andrewpatcarr/CV_OrigamiRobot_Fall2024/log_photos/joystick_arduino_housing.jpg

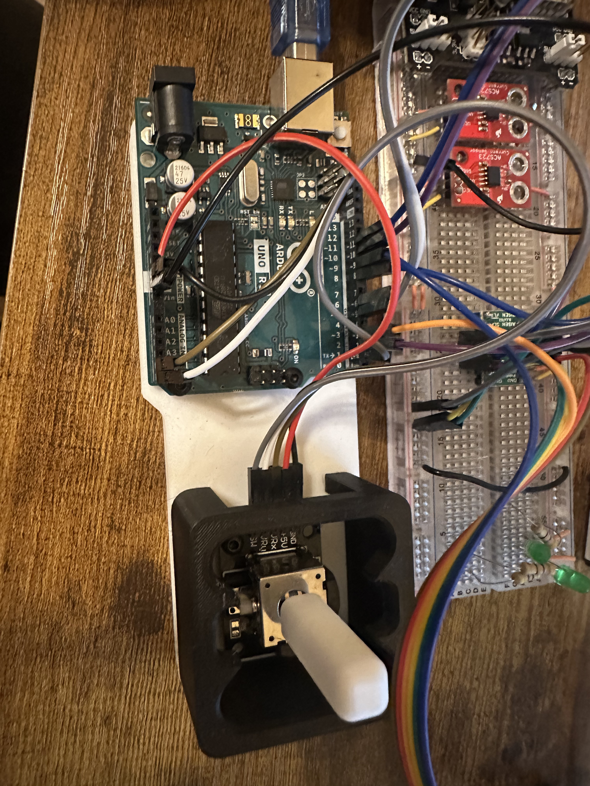
log_photos/joystick_arduino_housing.jpg
