andrewpatcarr/CV_OrigamiRobot_Fall2024/log_photos/motor_driver_screenshot_wordless.png

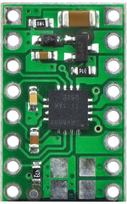
log_photos/motor_driver_screenshot_wordless.png
