andrewpatcarr/CV_OrigamiRobot_Fall2024/CAD/STLs/Friction Pads/Friction_straightangled_thinner^Worm_Robot.STL

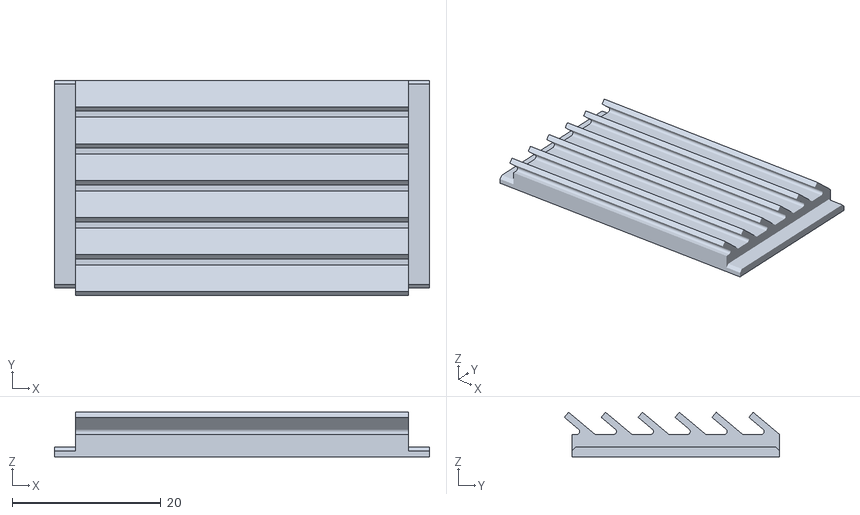
[picture p86: CAD file, 2024-11-07]
CAD/STLs/Friction Pads/Friction_straightangled_thinner^Worm_Robot.STL
50.5 x 29.0 x 6.00
