andrewpatcarr/CV_OrigamiRobot_Fall2024/CAD/SolidWorks/Pulley Horn^Worm_Robot.SLDPRT

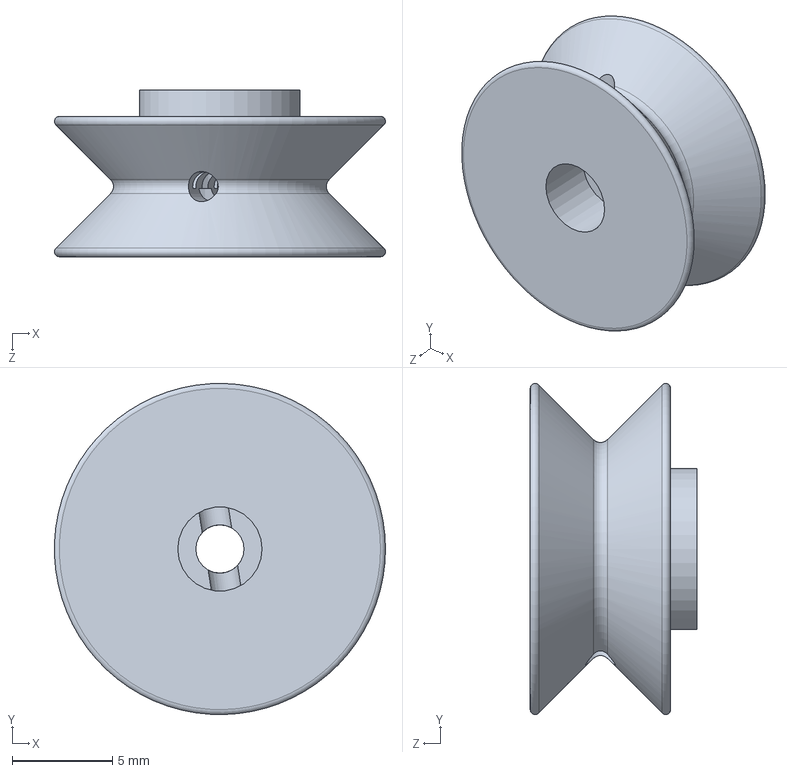
[picture p87: CAD file, 2024-10-20]
CAD/SolidWorks/Pulley Horn^Worm_Robot.SLDPRT
16.5 x 16.5 x 8.30 mm
