andrewpatcarr/CV_OrigamiRobot_Fall2024/CAD/SolidWorks/FS09R_Servo_Motor.SLDPRT

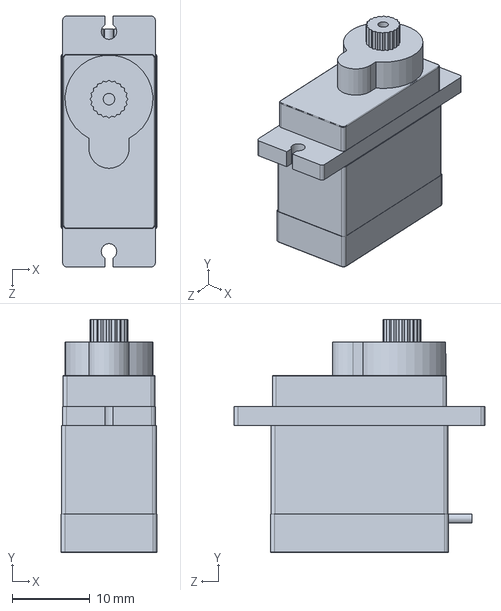
[picture p89: CAD file, 2024-10-16]
CAD/SolidWorks/FS09R_Servo_Motor.SLDPRT
12.3 x 30.0 x 32.2 mm
