andrewpatcarr/CV_OrigamiRobot_Fall2024/CAD/STLs/Friction Pads/Friction_straightangled_thinnest^Worm_Robot.STL

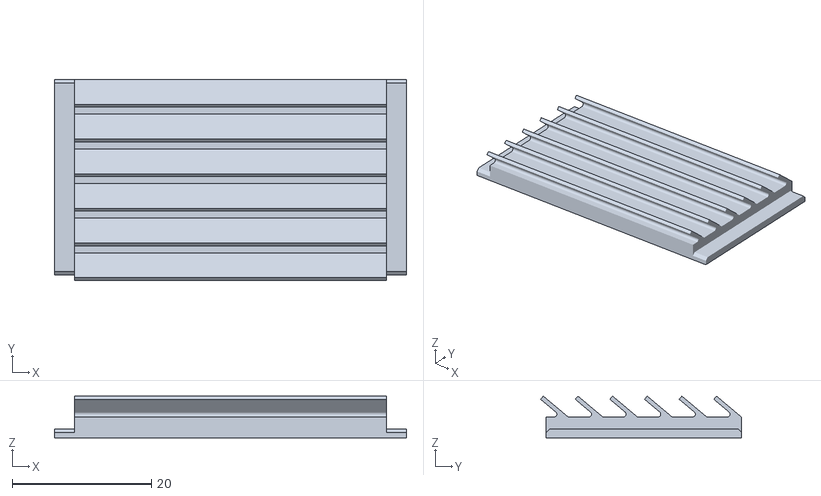
[picture p90: CAD file, 2024-11-07]
CAD/STLs/Friction Pads/Friction_straightangled_thinnest^Worm_Robot.STL
50.5 x 28.8 x 6.00
