andrewpatcarr/CV_OrigamiRobot_Fall2024/CAD/SolidWorks/Directional Friction Flexure_less.SLDPRT

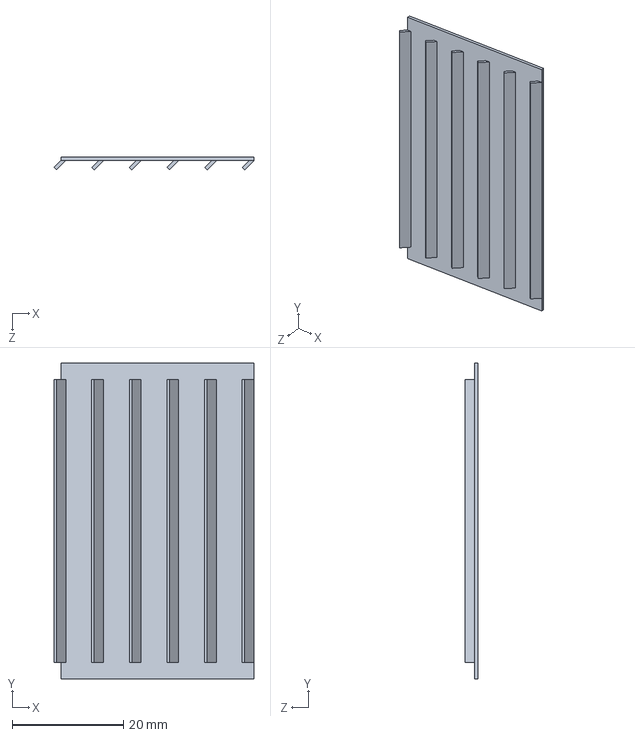
[picture p91: CAD file, 2024-10-15]
CAD/SolidWorks/Directional Friction Flexure_less.SLDPRT
35.9 x 56.8 x 2.30 mm
