andrewpatcarr/CV_OrigamiRobot_Fall2024/CAD/SolidWorks/Directional Friction Flexure.sldprt

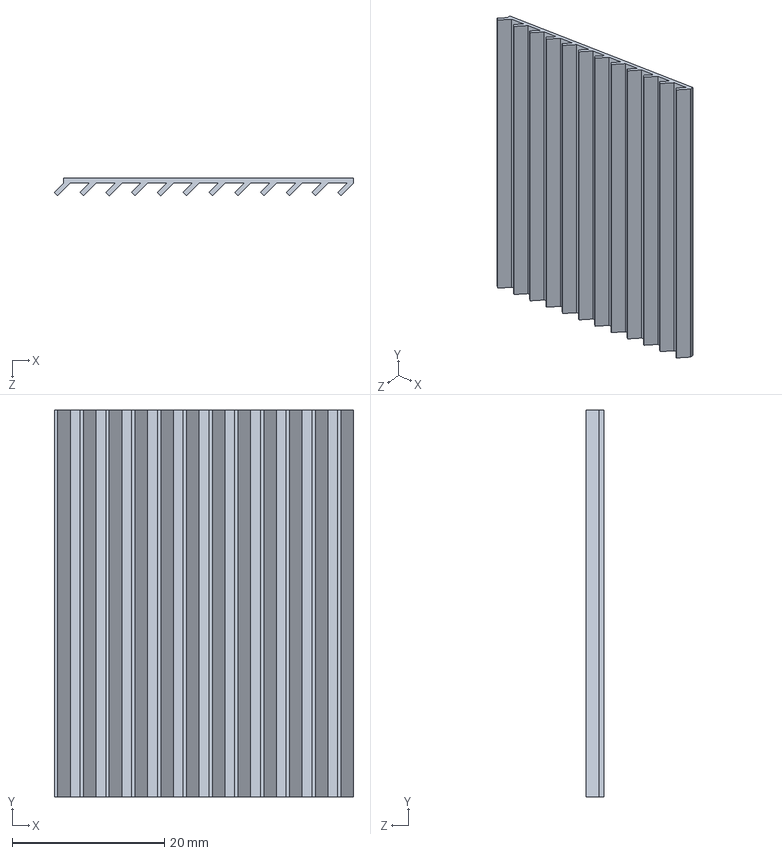
[picture p92: CAD file, 2024-10-14]
CAD/SolidWorks/Directional Friction Flexure.sldprt
39.3 x 50.8 x 2.30 mm
