andrewpatcarr/CV_OrigamiRobot_Fall2024/CAD/STLs/Mount Clamp Left^Worm_Robot.STL

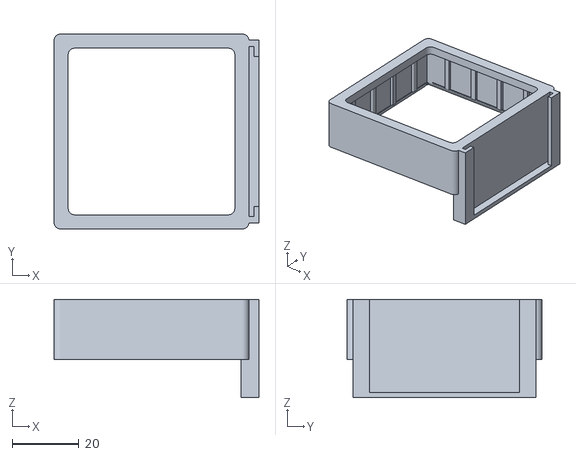
[picture p93: CAD file, 2024-10-19]
CAD/STLs/Mount Clamp Left^Worm_Robot.STL
61.5 x 58.5 x 29.5
