andrewpatcarr/CV_OrigamiRobot_Fall2024/CAD/SolidWorks/Directional Friction Pad.sldprt

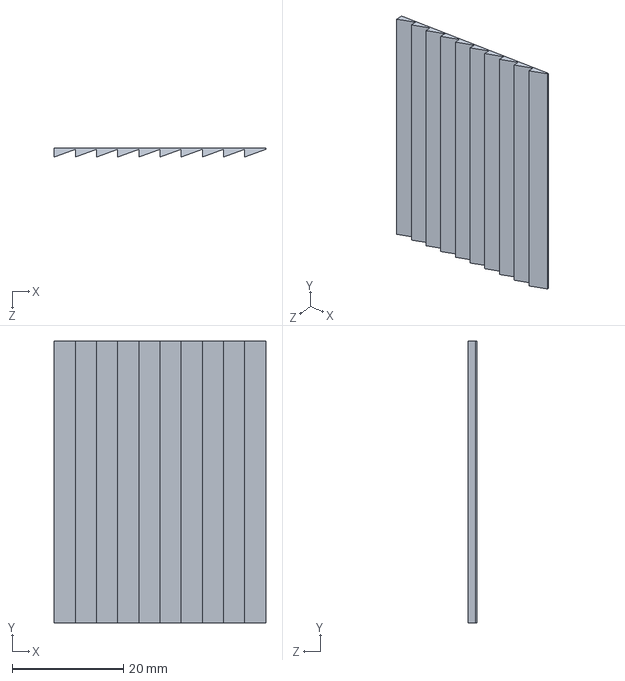
[picture p94: CAD file, 2024-10-13]
CAD/SolidWorks/Directional Friction Pad.sldprt
38.1 x 50.8 x 1.64 mm
