andrewpatcarr/CV_OrigamiRobot_Fall2024/CAD/STLs/Mount Clamp^Worm_Robot_walled.STL

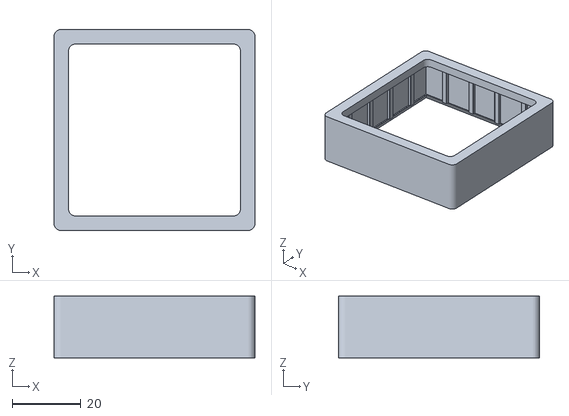
[picture p95: CAD file, 2024-10-15]
CAD/STLs/Mount Clamp^Worm_Robot_walled.STL
58.5 x 58.5 x 18.0
