andrewpatcarr/CV_OrigamiRobot_Fall2024/CAD/STLs/Directional Friction Flexure_og.STL

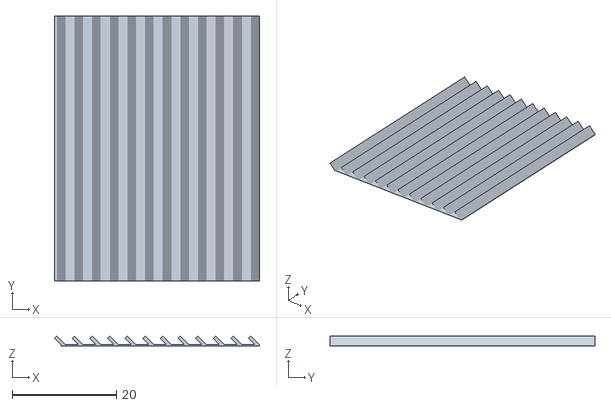
[picture p96: CAD file, 2024-10-14]
CAD/STLs/Directional Friction Flexure_og.STL
39.3 x 50.8 x 1.90
