andrewpatcarr/CV_OrigamiRobot_Fall2024/CAD/STLs/Mount Clamp^Worm_Robot.STL

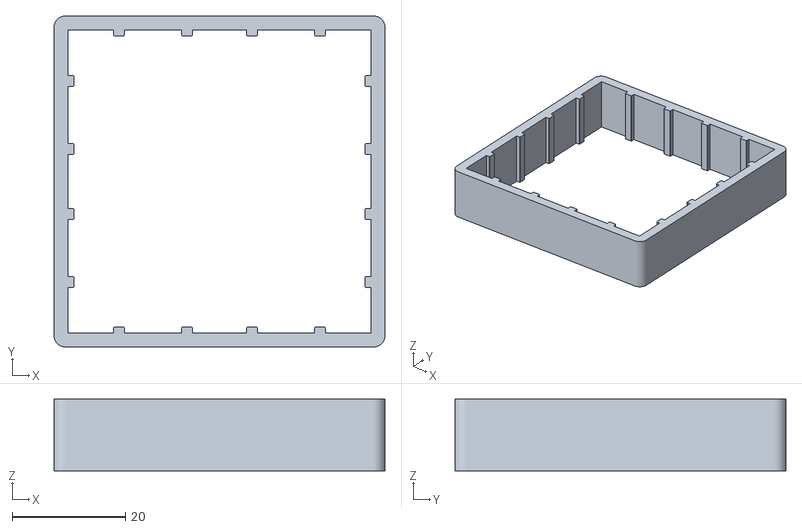
[picture p97: CAD file, 2024-10-13]
CAD/STLs/Mount Clamp^Worm_Robot.STL
58.5 x 58.5 x 12.7
