andrewpatcarr/CV_OrigamiRobot_Fall2024/CAD/SolidWorks/Worm_Robot.SLDASM

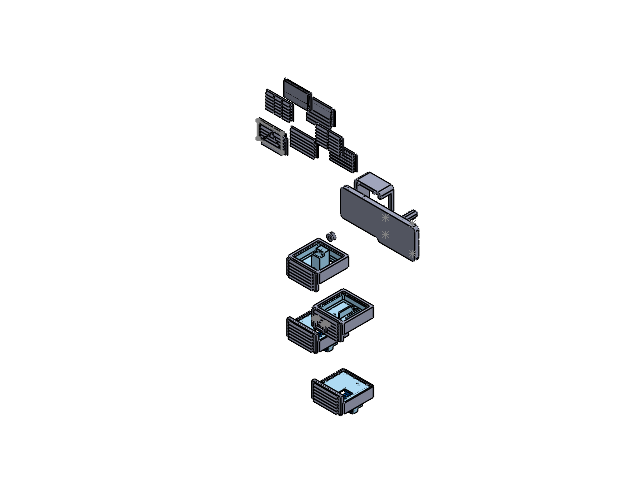
[picture p98: CAD file, 2024-12-04]
CAD/SolidWorks/Worm_Robot.SLDASM
Servo Motor Mounts x 3
Mount Clamp Right^Worm_Robot x 2
Mount Clamp Left^Worm_Robot x 2
FS09R_Servo_Motor x 2
Pulley Horn^Worm_Robot x 2
Friction_straightangled_og^Worm_Robot x 4
Joystick Base^Worm_Robot
Joystick Top^Worm_Robot
Gear box^Worm_Robot
Friction_straightangled_thinner^Worm_Robot
Friction_straightangled_thinnest^Worm_Robot
Friction_straightangled_sliced_half^Worm_Robot
Friction_straightangled_sliced_thirds^Worm_Robot
Friction_straightangled_triangled^Worm_Robot
Friction_straightangled_supersliced^Worm_Robot
Friction_straightangled_thinnest_raised^Worm_Robot
DC Motor Mount
DC Clamp^Worm_Robot
DC Pulley
Friction_straightangled_thinnest_long^Worm_Robot
