andrewpatcarr/CV_OrigamiRobot_Fall2024/Programming/train_test/runs/detect/predict2/IMG_1269_jpeg.rf.be2bfbd61c21fc8621fb3a13257b4607.jpg

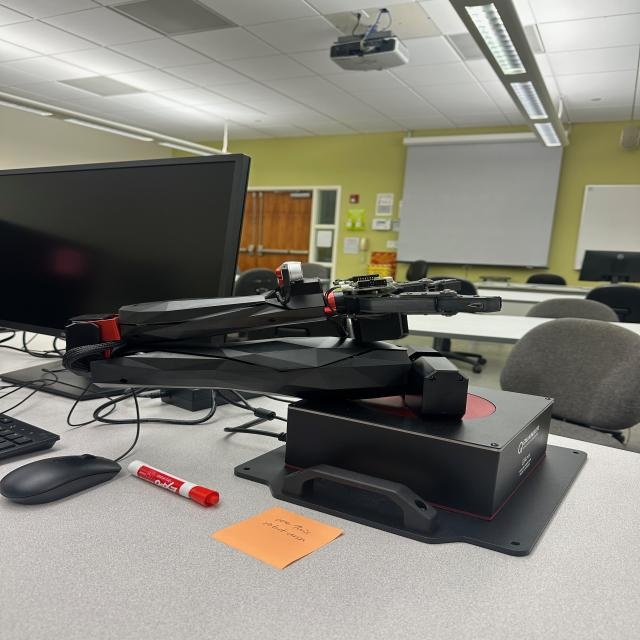
Programming/train_test/runs/detect/predict2/IMG_1269_jpeg.rf.be2bfbd61c21fc8621fb3a13257b4607.jpg
