andrewpatcarr/CV_OrigamiRobot_Fall2024/Programming/train_test/runs/detect/predict/bus.jpg

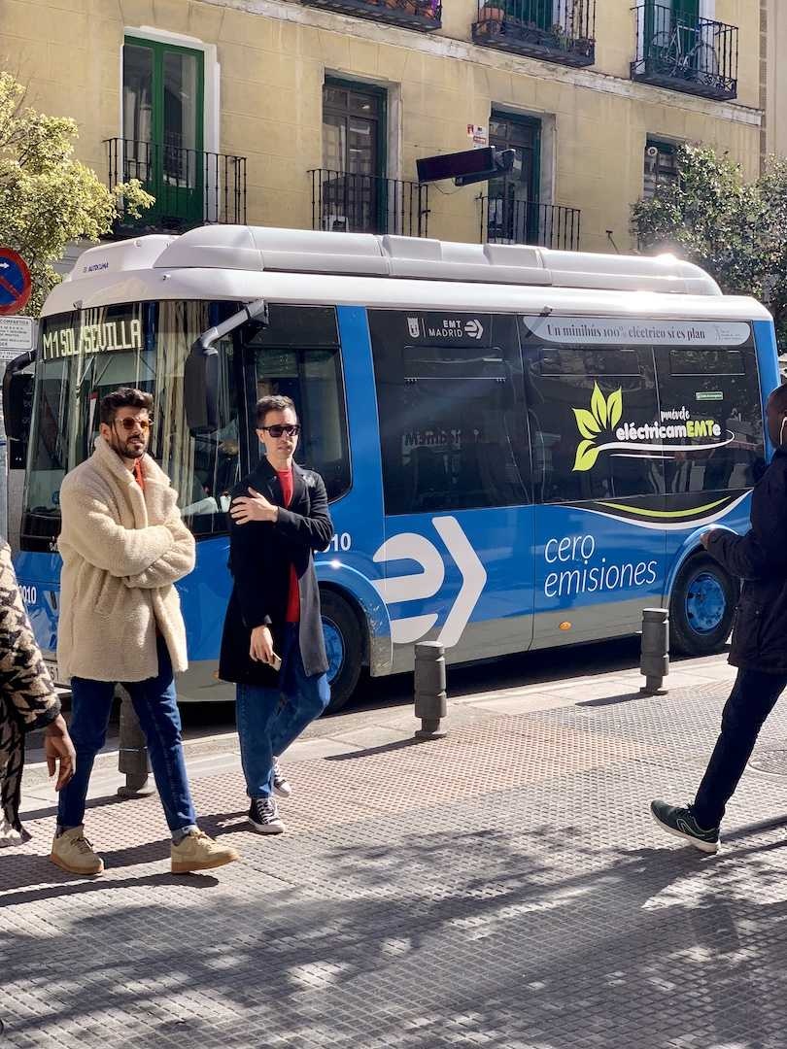
Programming/train_test/runs/detect/predict/bus.jpg
