andrewpatcarr/CV_OrigamiRobot_Fall2024/Programming/train_test/runs/detect/train4/train_batch31.jpg

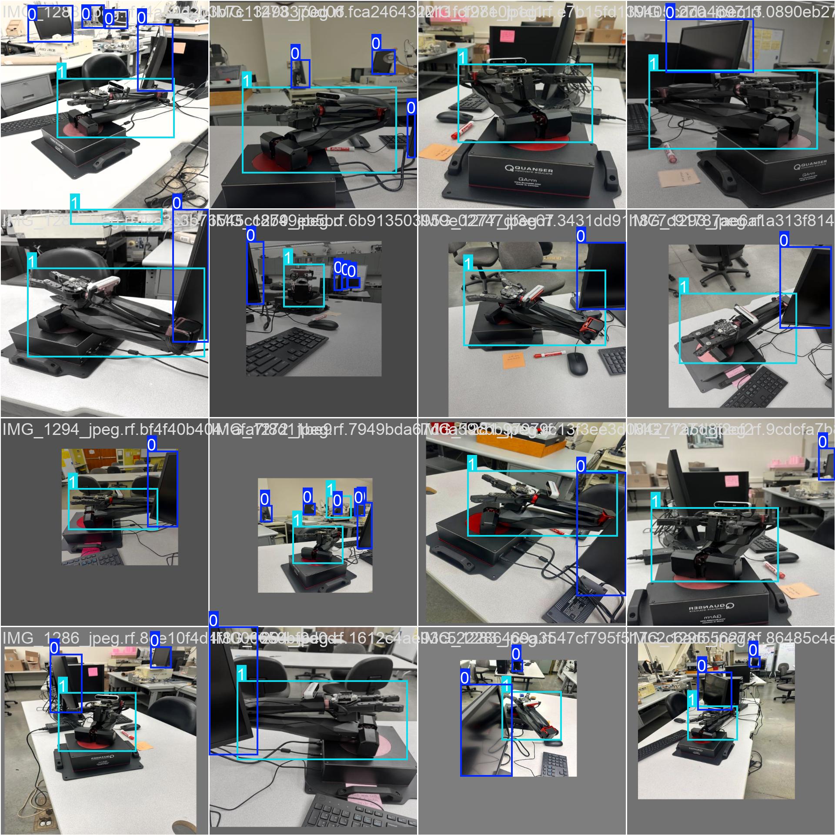
Programming/train_test/runs/detect/train4/train_batch31.jpg
