andrewpatcarr/CV_OrigamiRobot_Fall2024/Programming/train_test/runs/detect/train7/train_batch1000.jpg

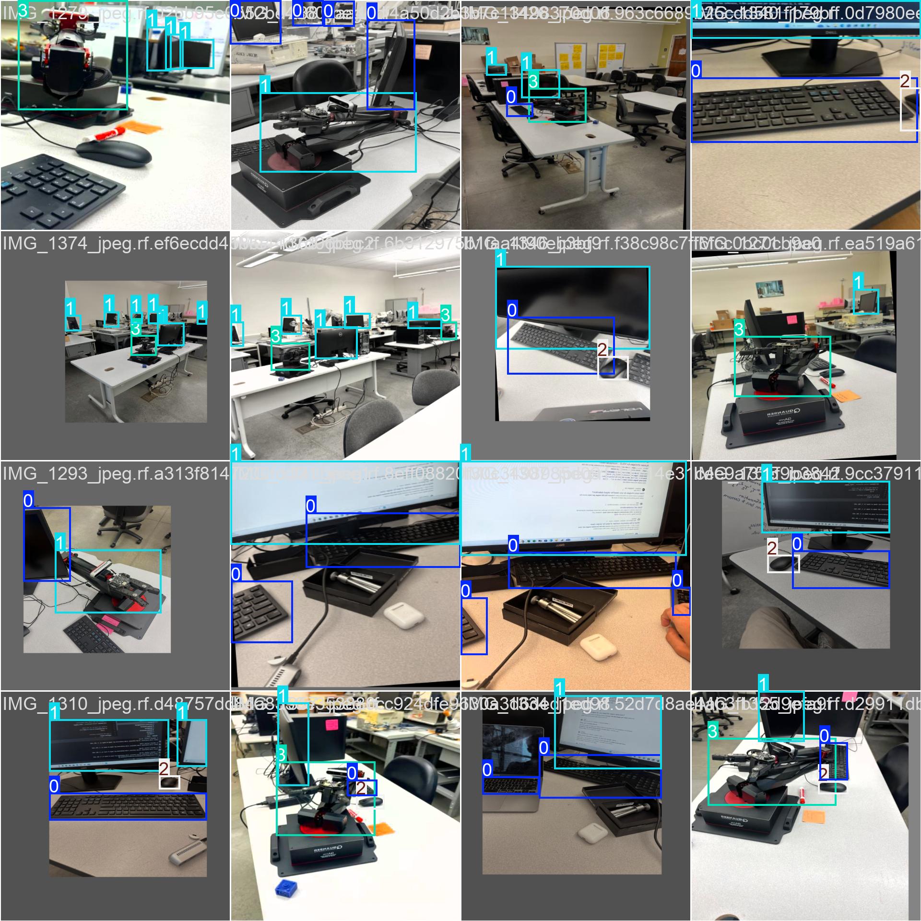
Programming/train_test/runs/detect/train7/train_batch1000.jpg
