andrewpatcarr/CV_OrigamiRobot_Fall2024/Programming/train_test/runs/detect/train12/confusion_matrix_normalized.png

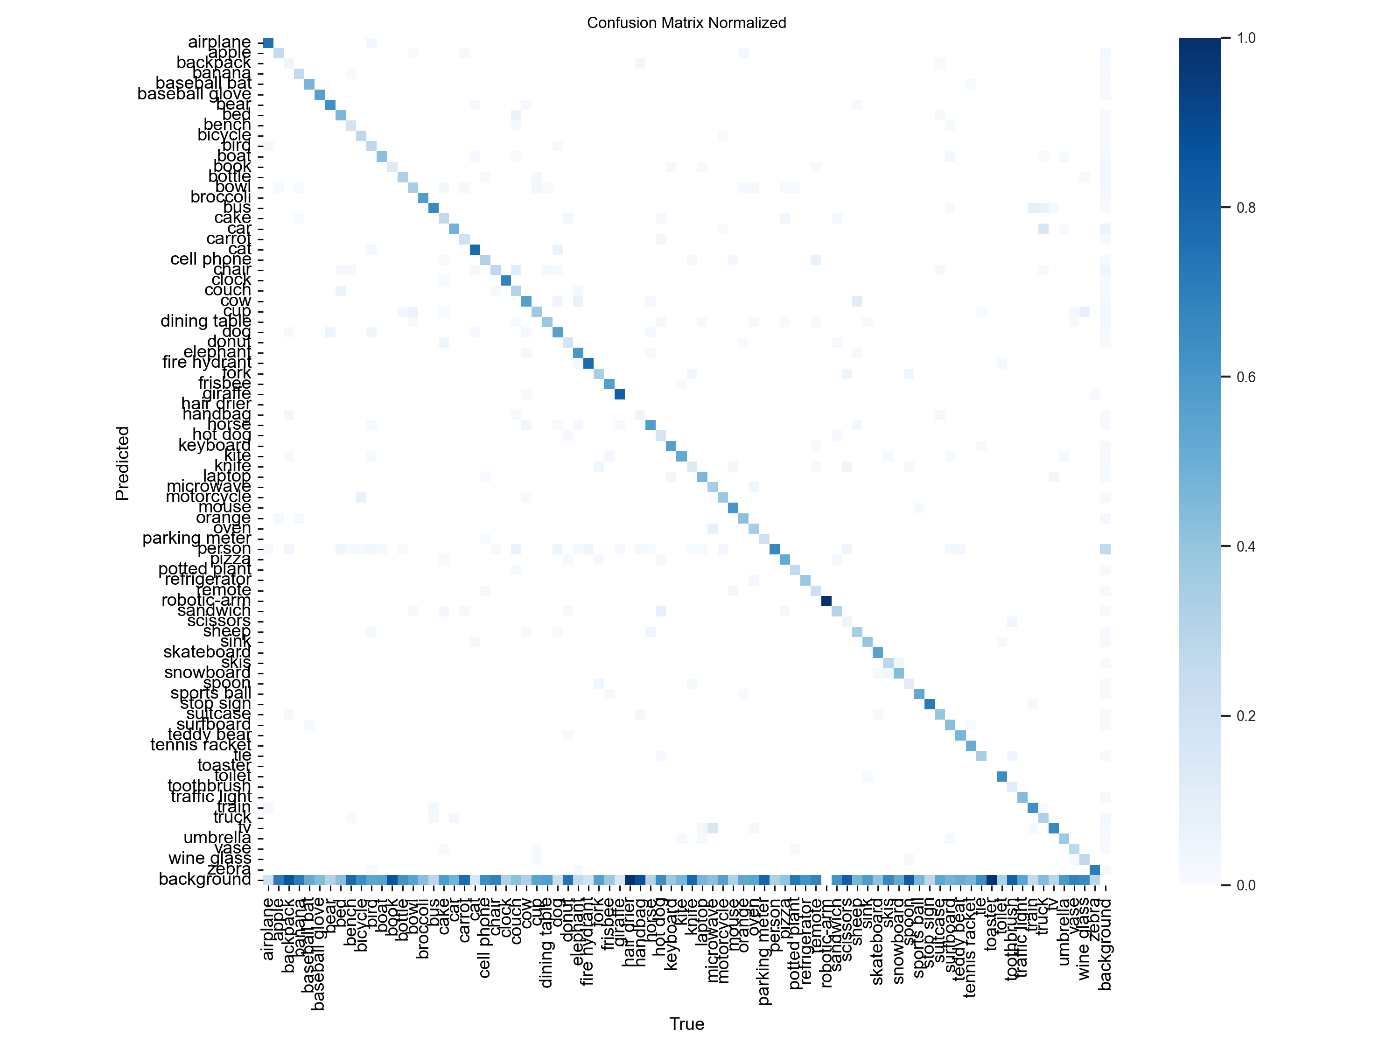
Programming/train_test/runs/detect/train12/confusion_matrix_normalized.png
