andrewpatcarr/CV_OrigamiRobot_Fall2024/Programming/train_test/runs/detect/train12/F1_curve.png

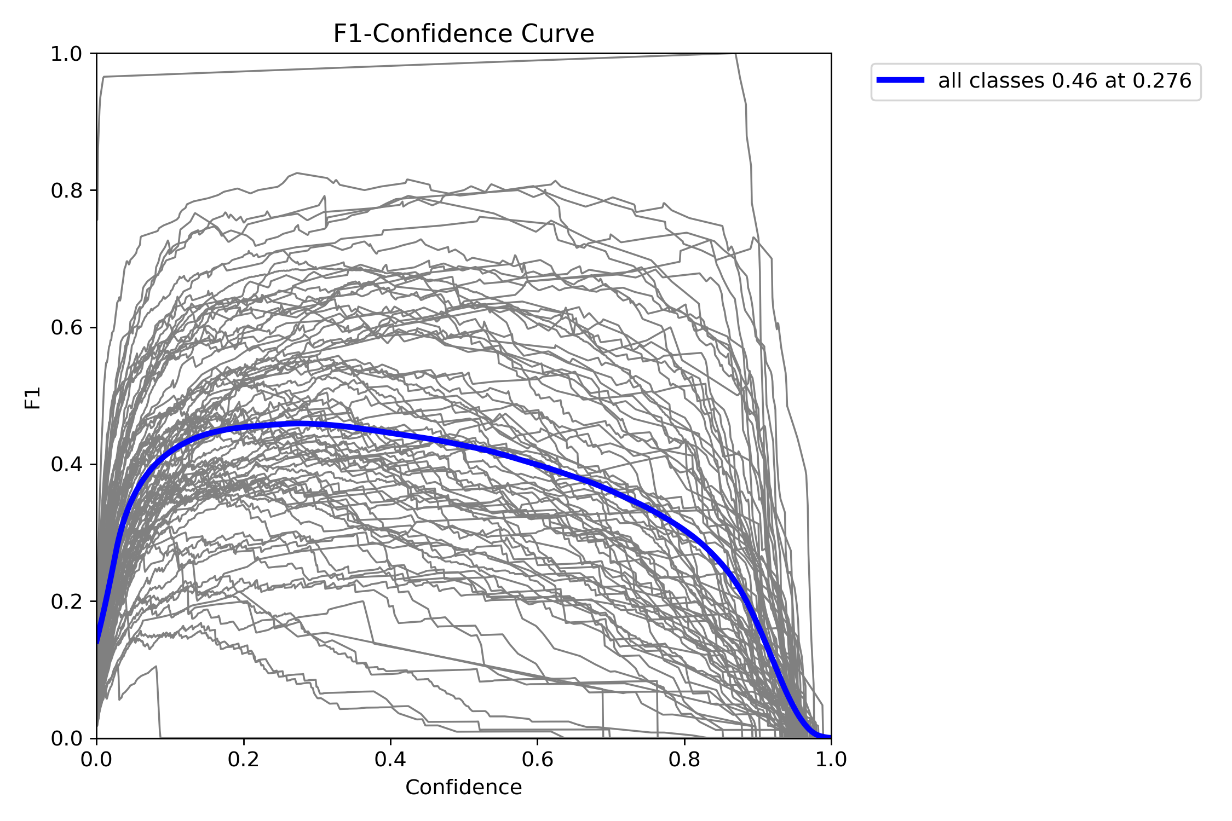
Programming/train_test/runs/detect/train12/F1_curve.png
