andrewpatcarr/CV_OrigamiRobot_Fall2024/Programming/train_test/runs/detect/train12/train_batch2.jpg

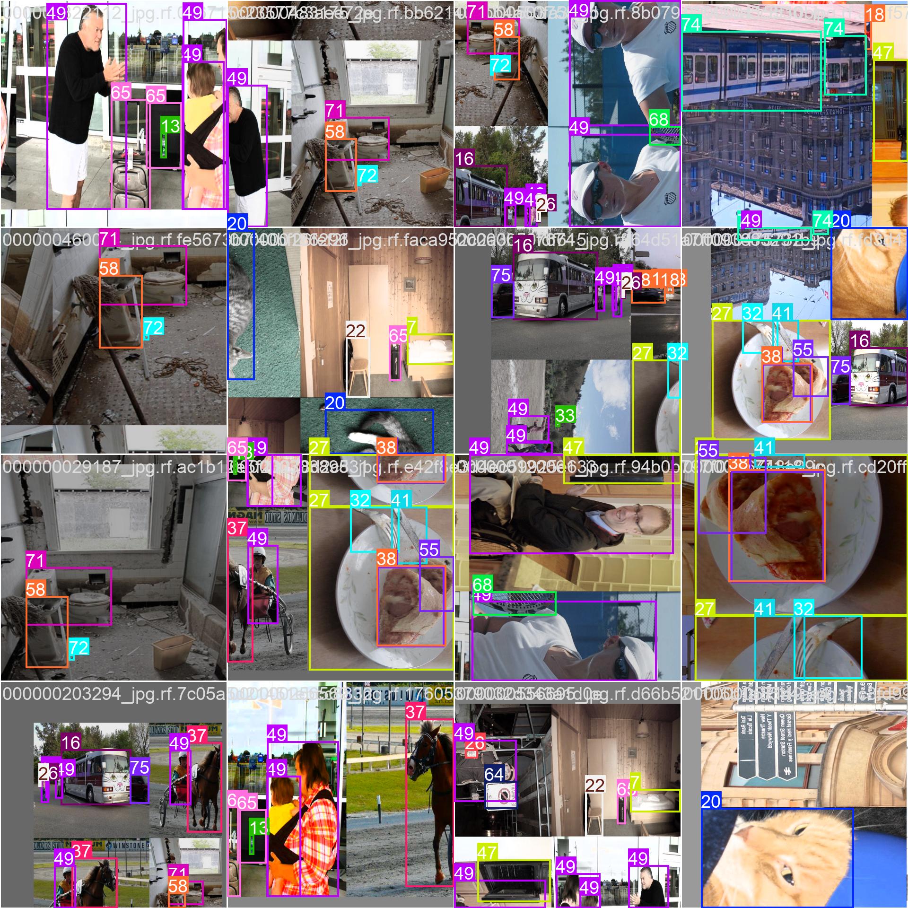
Programming/train_test/runs/detect/train12/train_batch2.jpg
