andrewpatcarr/CV_OrigamiRobot_Fall2024/Programming/train_test/runs/detect/train12/train_batch50962.jpg

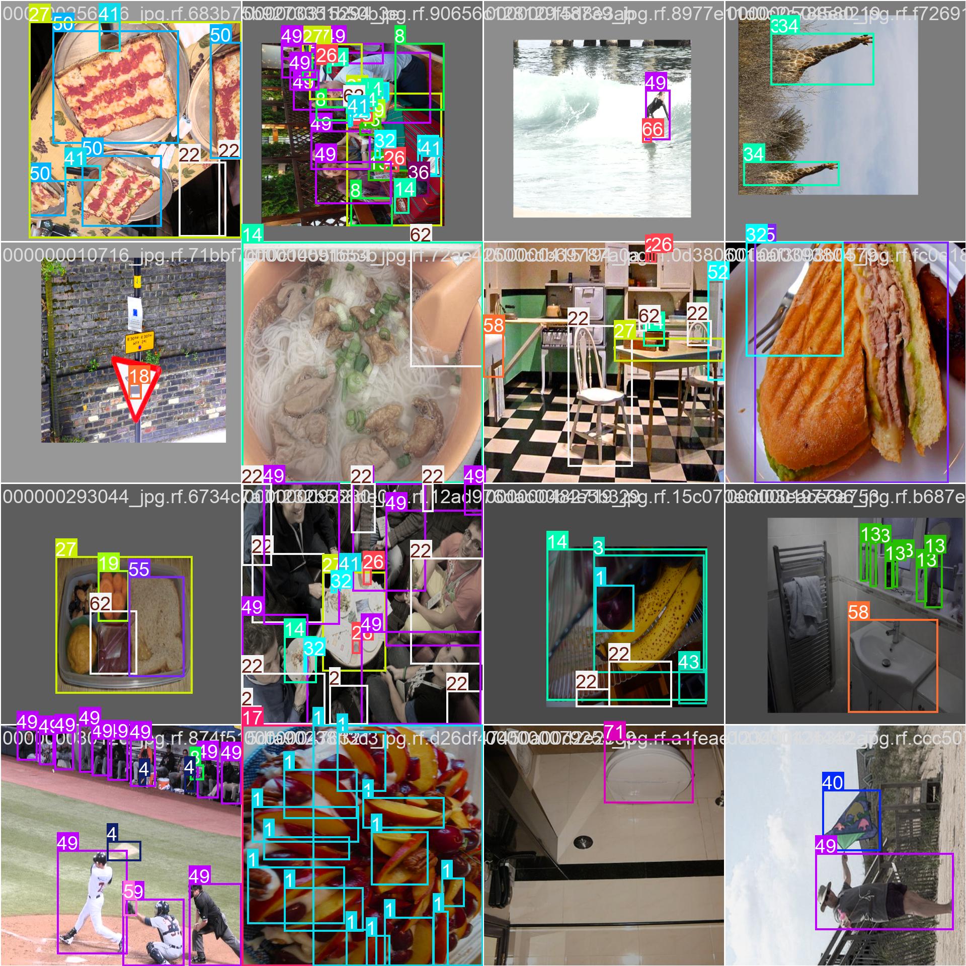
Programming/train_test/runs/detect/train12/train_batch50962.jpg
