andrewpatcarr/CV_OrigamiRobot_Fall2024/Programming/train_test/runs/detect/train12/val_batch1_labels.jpg

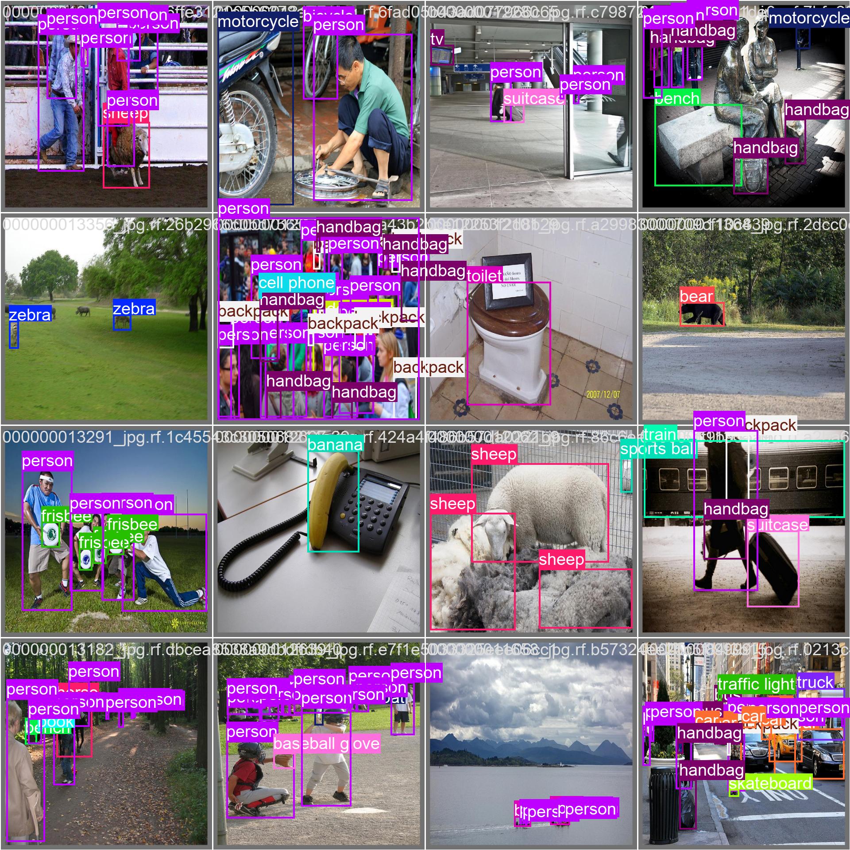
Programming/train_test/runs/detect/train12/val_batch1_labels.jpg
