andrewpatcarr/CV_OrigamiRobot_Fall2024/Programming/train_test/runs_compare1/segment/predict/comparison_image1.jpeg

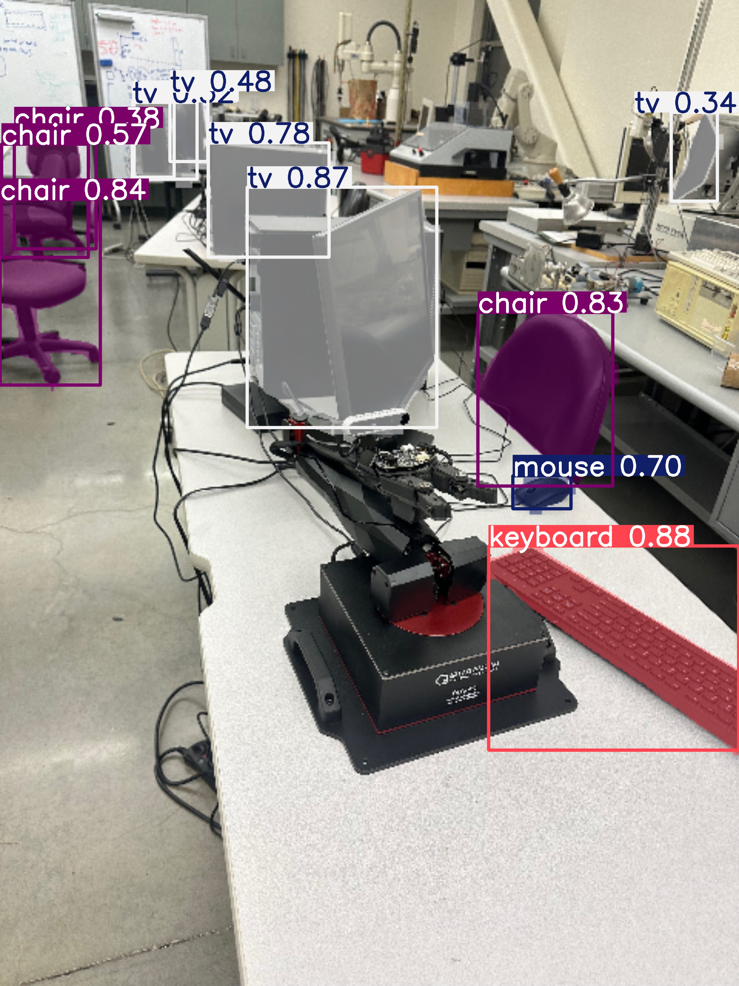
Programming/train_test/runs_compare1/segment/predict/comparison_image1.jpeg
